rubenoxen/RootMixer/firmware/inc/tusb_config.h

#ifndef _TUSB_CONFIG_H_
#define _TUSB_CONFIG_H_

#ifdef __cplusplus
extern "C" {
#endif

#define CFG_TUSB_MCU               OPT_MCU_STM32F4
#define CFG_TUSB_RHPORT0_MODE      (OPT_MODE_DEVICE | OPT_MODE_FULL_SPEED)
#define CFG_TUSB_OS                OPT_OS_NONE

#define CFG_TUD_ENDPOINT0_SIZE     64
#define CFG_TUD_MIDI               1
#define CFG_TUD_MIDI_RX_BUFSIZE    64
#define CFG_TUD_MIDI_TX_BUFSIZE    64

#ifdef __cplusplus
}
#endif

#endif
